Hans-Beerman/nodevoordeurnw/Photos/20231104_163537.jpg

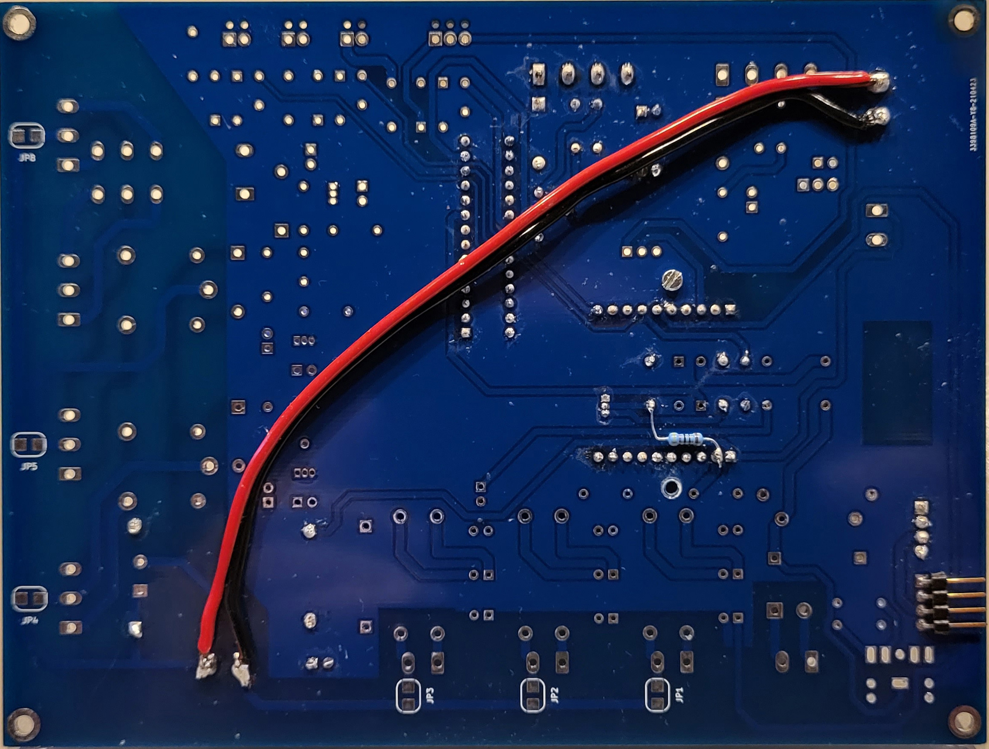
Photos/20231104_163537.jpg
