Hans-Beerman/nodevoordeurnw/Photos/20231102_201735.jpg

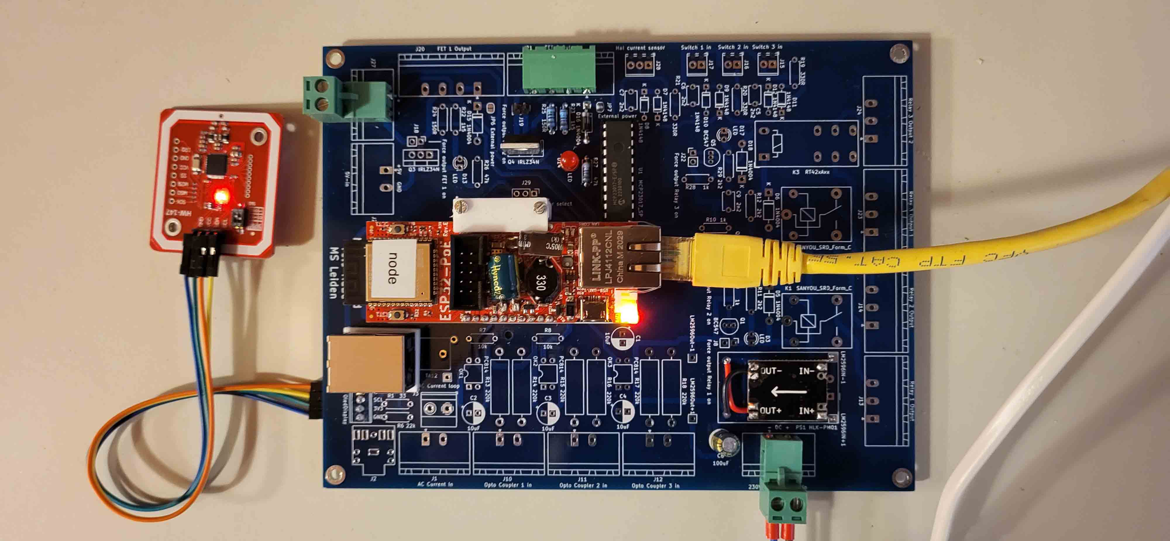
Photos/20231102_201735.jpg
