Hans-Beerman/nodevoordeurnw/Photos/20231102_201757.jpg

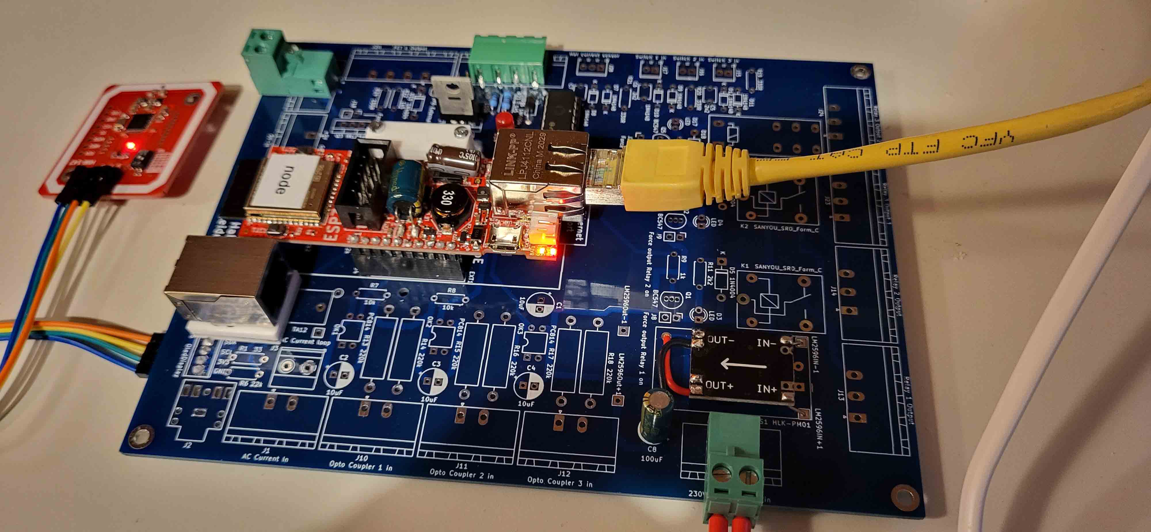
Photos/20231102_201757.jpg
