Hans-Beerman/nodevoordeurnw/Photos/20231104_163352.jpg

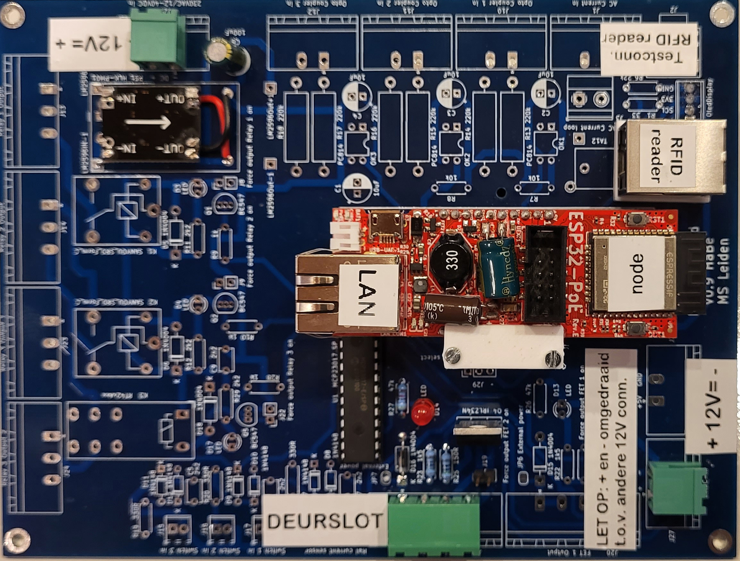
Photos/20231104_163352.jpg
