Hans-Beerman/nodevoordeurnw/Photos/20231104_163704.jpg

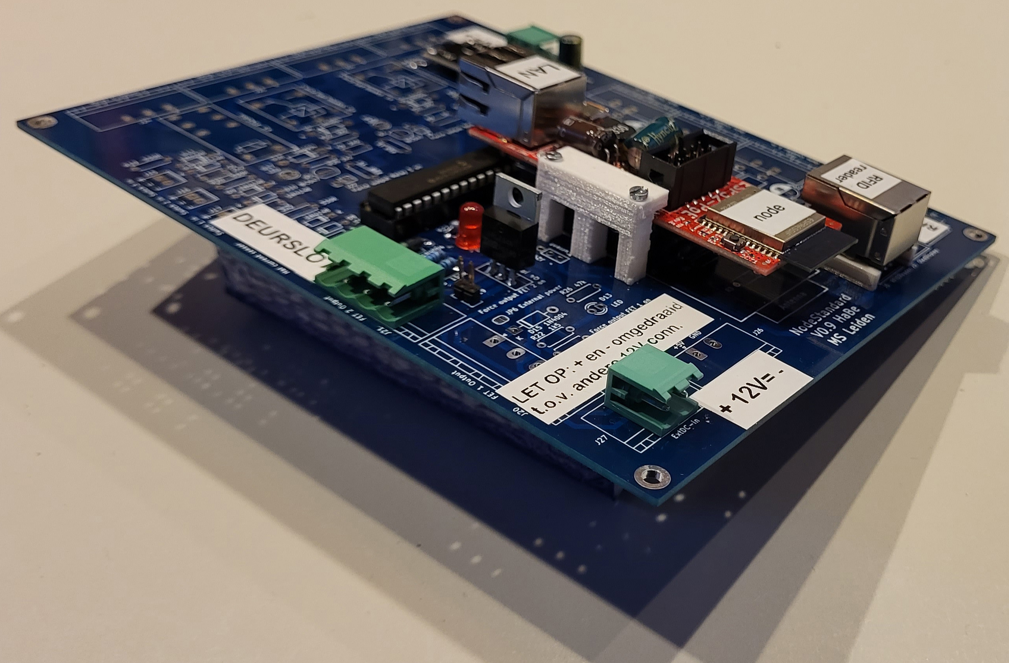
Photos/20231104_163704.jpg
