Hans-Beerman/nodevoordeurnw/Photos/20231104_163852.jpg

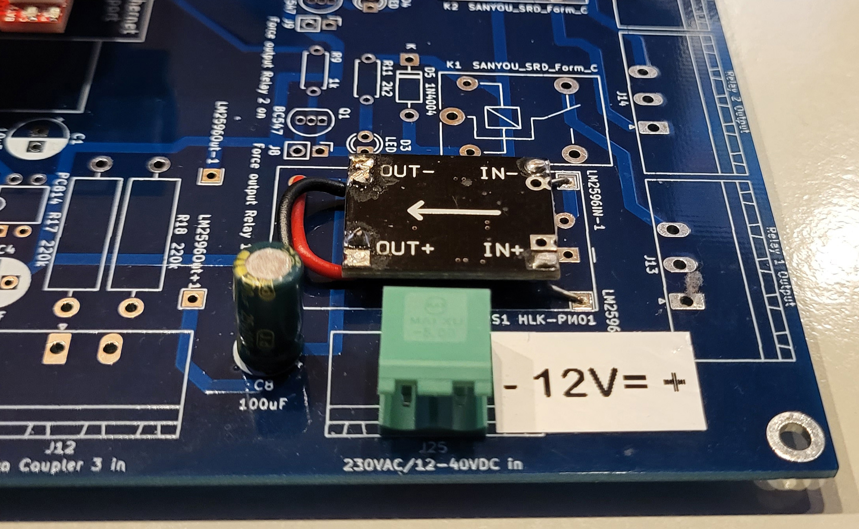
Photos/20231104_163852.jpg
